DeuceEFI/Cruiser/pcb/Cruiser.sch

## KiCad design pcb/Cruiser.sch (2013-04-03)

Schematic: Cruiser.sch

Parts:
C1, C2, C3: 0.1uF
C4, C5, C6, C7, C8, C9, C10: 0.22uF
C11: 10uF
C12, C13: 20pF
C14: 6.8nF
C15: 680pF
D1, D2, D3: LED
H1: Hole
J1: USB-A
L1: 40
P1: BDM
P2: GND-T0-T1-T2-T3
R1, R2, R3, R4, R5, R6: 10k
R7, R8, R11, R12, R13, R14, R15, R16: 1k
R10: 3.3k
SW1: Load
SW2: Reset
SW3, SW4, SW5: SOLDER_BRIDGE
U1: FT232RL
U2: MC9S12XDP512; mc9s12xdp512-LQFP112
X1: 16MHz

Notes on the sheet:
Keychain Hole
USB to TTL Serial Communications
10v Tantalum
X7R Ceramic
Load/Run LED
BDM Connector
PLL Circuit
Crystal Circuit
Load SW1: Open = Run Closed = Load
CPU Pin 43
CPU Pin 44
CPU Pin 45
The board is powered completely by the USB port, so no external power supply is needed.
This goal of this project is to develop a small portable development board you can carry with you to develop code against.
